stangtr/SDR_Project_TravisStefan/LTSpice_Simulation/BandPass.asc

C1: cap; 5.1n
C2: cap; 5.1n
C3: cap; 4.7n
L1: ind; 6.2µ
L2: ind; 6.2µ
L3: ind; 6.2µ
R1: res; 50
R2: res; 50
V1: voltage; ""; AC 2
Named nets: 0
.ac dec 10000 400k 1700k
