stangtr/SDR_Project_TravisStefan/LTSpice_Simulation/Receiver.asc

C1: cap; 4.3n
C2: cap; 4.3n
C3: cap; 5.1n
C4: cap; 10µ
C5: cap; .1µ
C6: cap; 10µ
C7: cap; 750p
C8: cap; 750p
C9: cap; .1µ
C10: cap; 10p
C11: cap; 10µ
C12: cap; 750p
C13: cap; 750p
C14: cap; 10p
C15: cap; 100p
C16: cap; 220p
C17: cap; 100p
C18: cap; 220p
L1: ind; 6.2µ
L2: ind; 6.2µ
L3: ind; 5.1µ
R1: res; 10k
R2: res; 50
R3: res; 10k
R4: res; 10k
R5: res; 10k
R6: res; 24.7k
R7: res; 100
R8: res; 24.7k
R9: res; 10k
R10: res; 10k
R11: res; 55k
R12: res; 1k
R13: res; 1k
R14: res; 10k
R15: res; 10k
R16: res; 24.7k
R17: res; 100
R18: res; 24.7k
R19: res; 10k
R20: res; 10k
R21: res; 55k
R22: res; 8.2k
R23: res; 15k
R24: res; 8.2k
R25: res; 15k
S1: sw; MYSW
S2: sw; MYSW
S3: sw; MYSW
S4: sw; MYSW
U1: opamp2; lm358
U2: opamp2; lm358
U3: opamp2; lm358
U4: opamp2; lm358
U5: opamp2; lm358
U6: opamp2; lm358
U7: opamp2; lm358
U8: opamp2; lm358
V1: voltage; SINE(0 {sigV} {sigF}); AC 2
V2: voltage; 4.3
V3: voltage; SINE(0 50 {f} 0 0 0)
V4: voltage; SINE(0 50 {f} 0 0 90)
V5: voltage; SINE(0 50 {f} 0 0 180)
V6: voltage; SINE(0 50 {f} 0 0 270)
V7: voltage; 4.3
V8: voltage; 4.3
Named nets: 0, s1, s2, s3, s4, 0_deg, 90_deg, 180_deg, 270_deg, AGND, +5, REF2.5, I, Q
;ac dec 1000000 40k 100000000
.tran 0 20m 0 .1u
.model MYSW SW(Ron=15 Roff=10G Vt={sigV*0.707} Vh=0)
.param f=1060e3
.lib lm358.sub
.param sigF=1070e3
Note: Make sure to put sampling capacitors in parallel with the 0 90 180 270 outputs making the impedence 200
Note: Use Sine waves, incoming freq - LO = 10kHz
;tran 0 100m 0 100u
.param sigV=1m
